kc8nod/RobotKnifeFight/doc/assembled_bot-0102.png

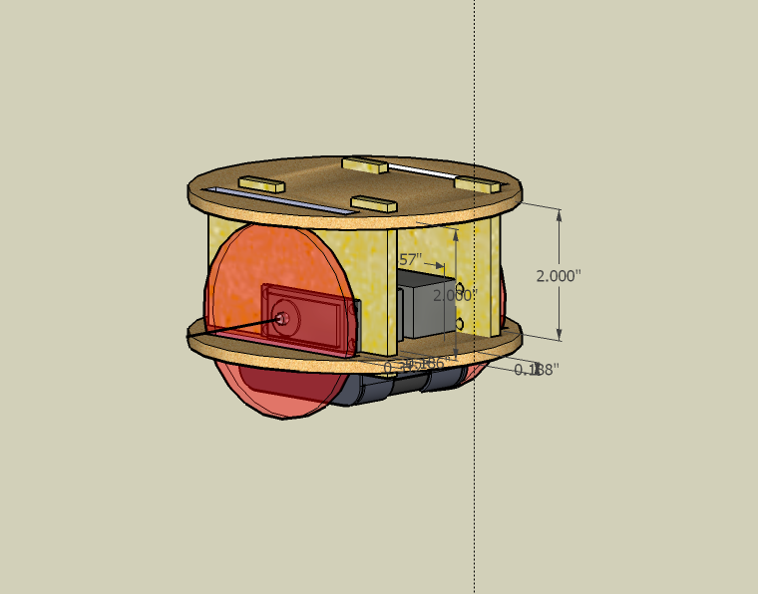
doc/assembled_bot-0102.png
